92Garfield/LED-Strip-Software/PCB/simplified/4-strips, 4-power/case/v1/preview_assembly.png

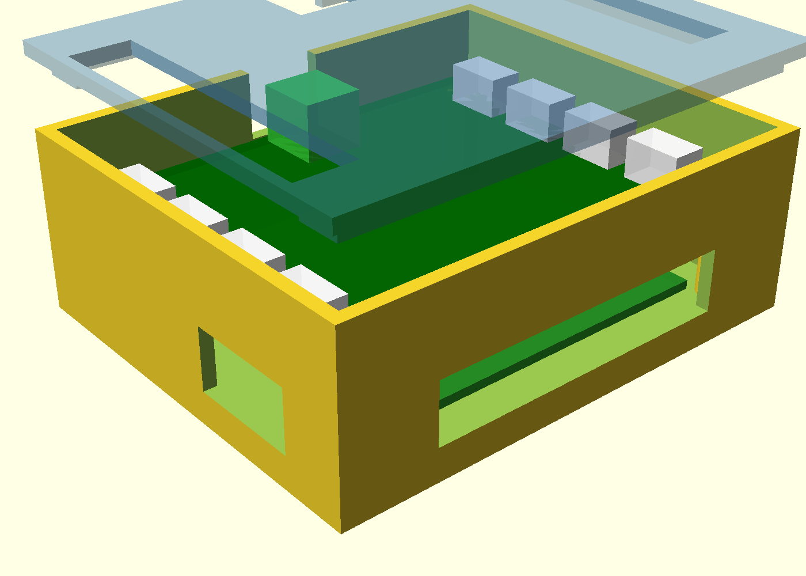
PCB/simplified/4-strips, 4-power/case/v1/preview_assembly.png
